YugAjmera/ALFA/images/2.jpg

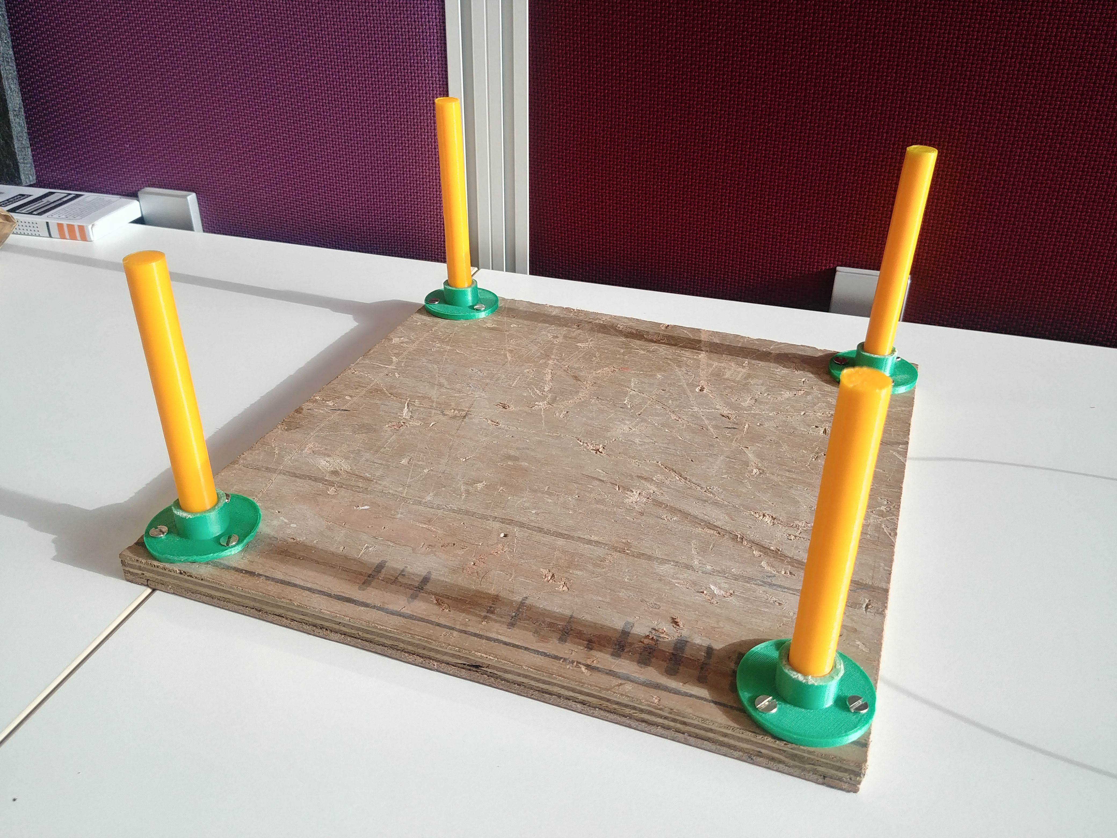
images/2.jpg
