YugAjmera/ALFA/images/3.jpg

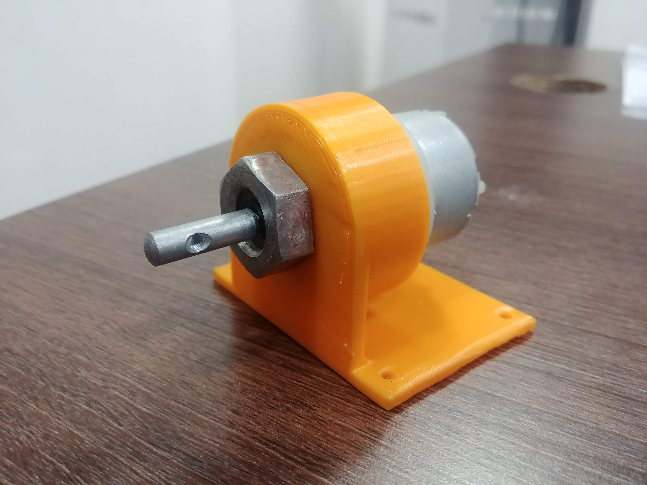
images/3.jpg
