YugAjmera/ALFA/images/20190709_175455.jpg

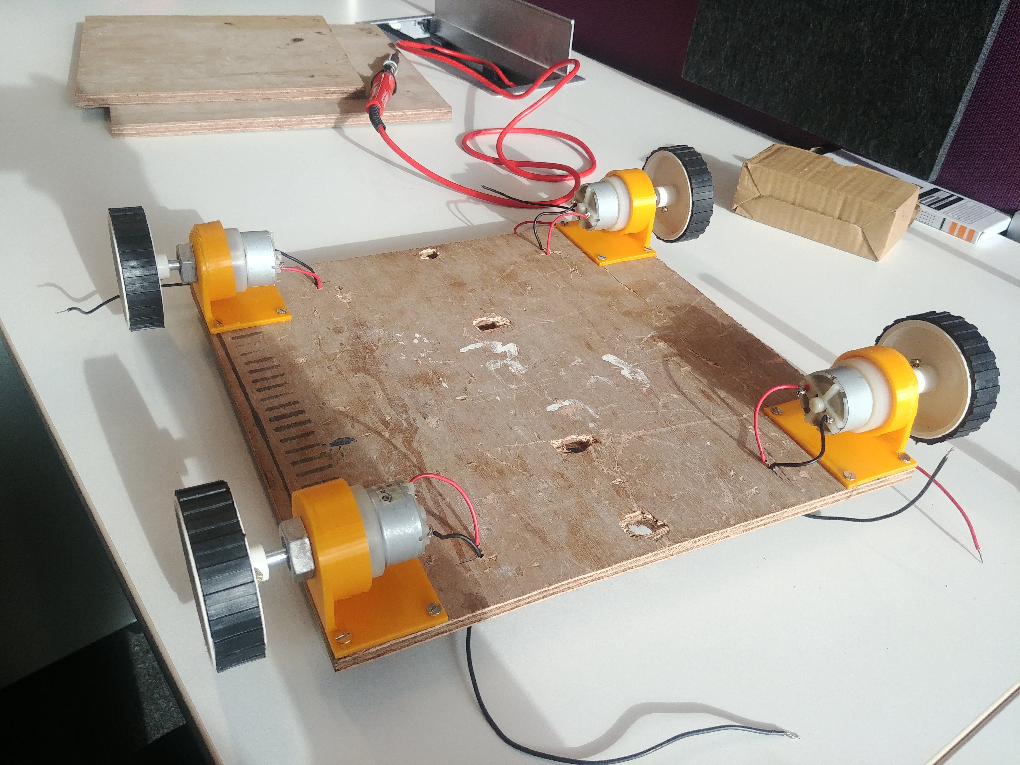
images/20190709_175455.jpg
