YugAjmera/ALFA/images/20190709_193052.jpg

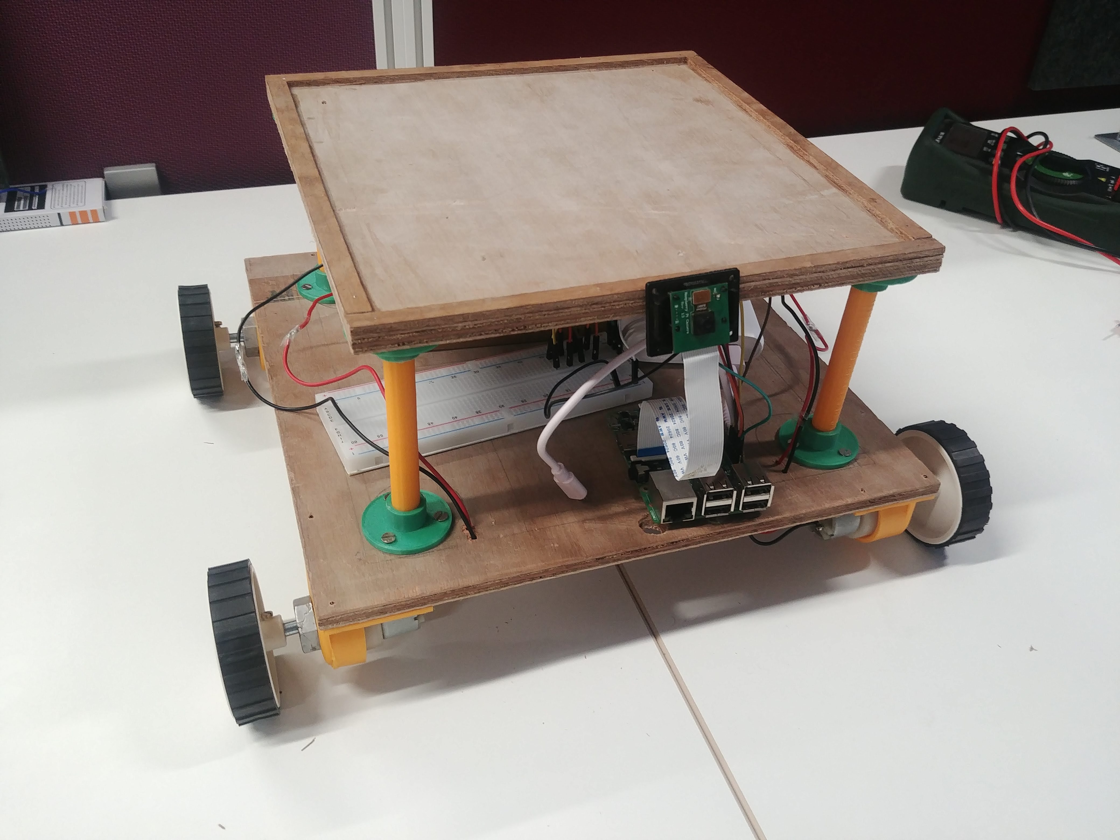
images/20190709_193052.jpg
