YugAjmera/ALFA/images/support_rod_mount.jpg

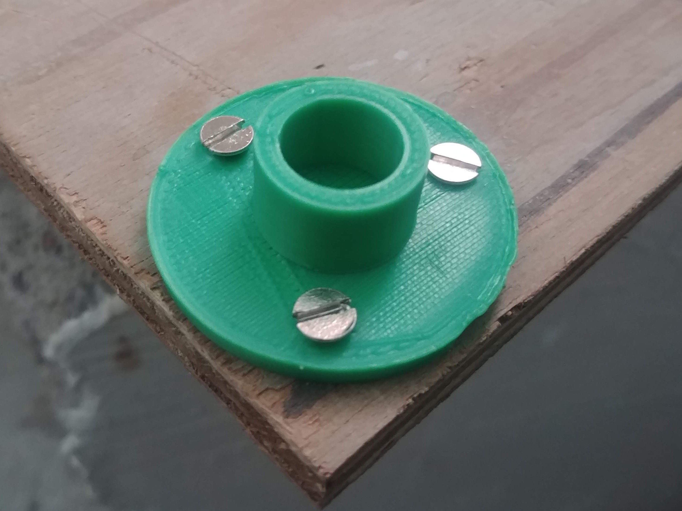
images/support_rod_mount.jpg
