YugAjmera/ALFA/CAD files/Parts/support_rod_floor_1.JPG

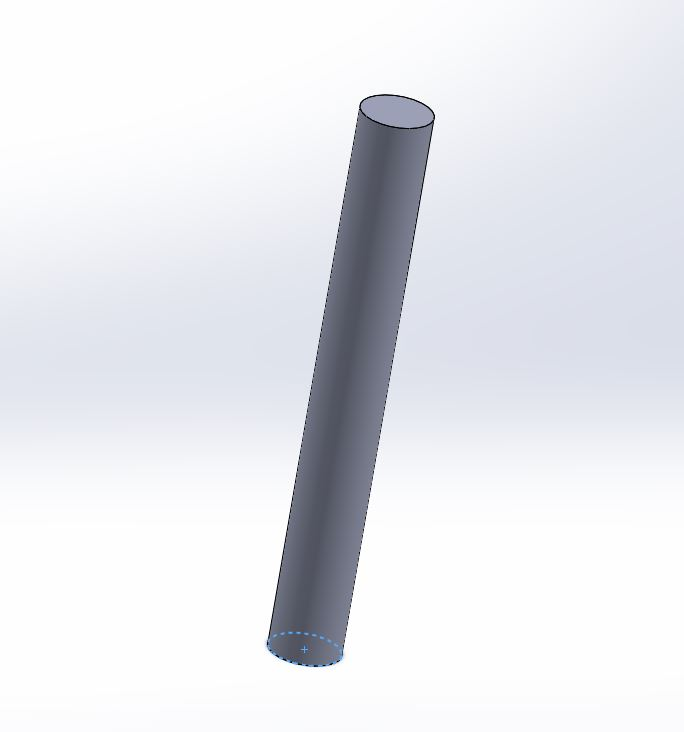
CAD files/Parts/support_rod_floor_1.JPG
