YugAjmera/ALFA/images/20190709_184045.jpg

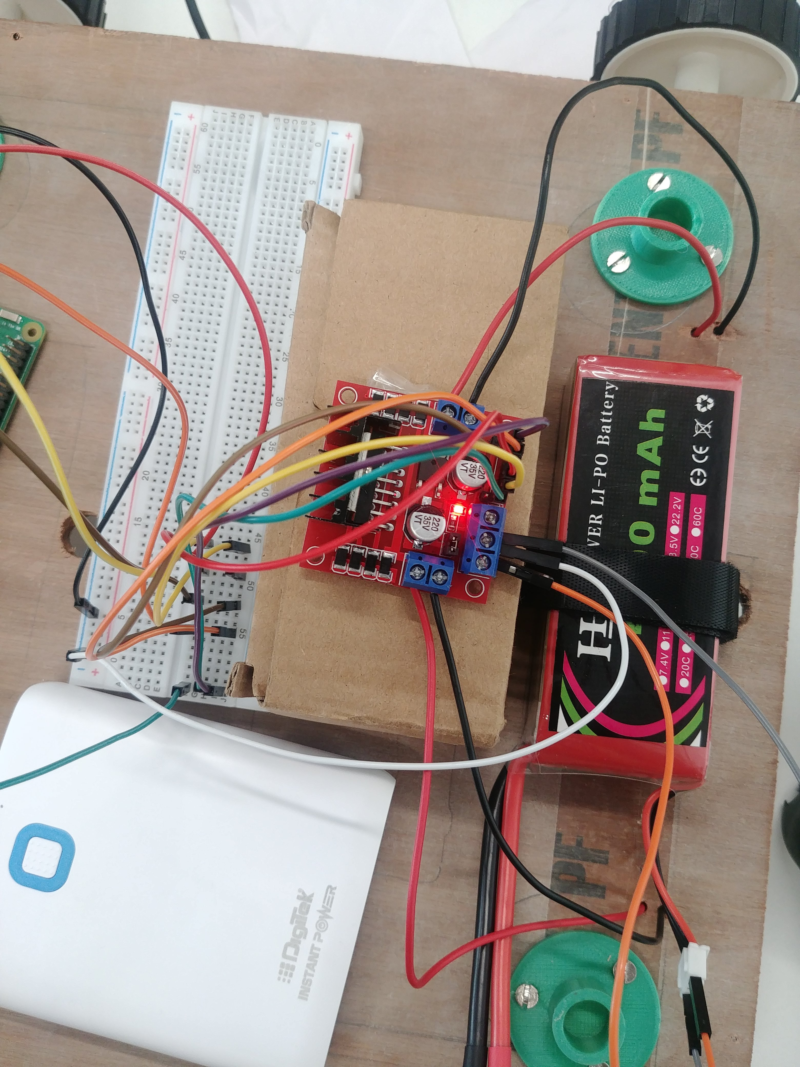
images/20190709_184045.jpg
