YugAjmera/ALFA/images/IMG_20190713_134319837.jpg

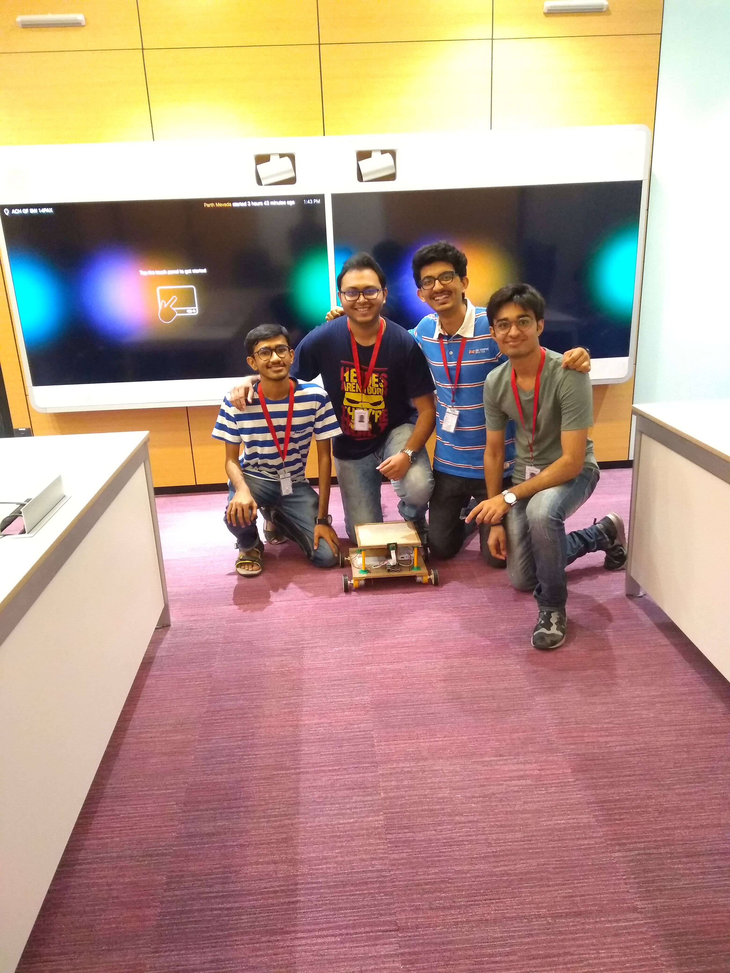
images/IMG_20190713_134319837.jpg
